devices-lab/solderbit-segment-shift-edition/assembly/step_06_DIP.png

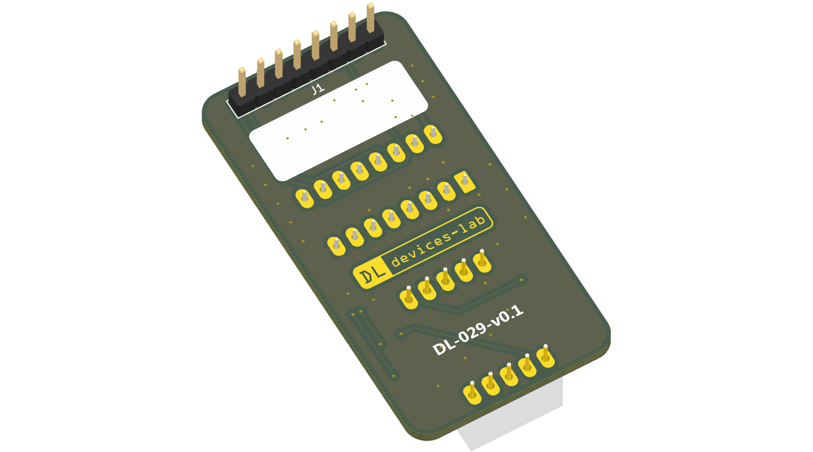
assembly/step_06_DIP.png
